Moryu-Io/Bldc_Servo_Driver_Prj/common/ExtInterface/ext_com_define.hpp

#ifndef EXT_COM_DEFINE_HPP
#define EXT_COM_DEFINE_HPP

#include "main.h"

#define IS_REQ_STATUS_SUMMARY(x) ((x & 0x8000) == 0x8000) // REQのCMDIDに15bit目が立っている場合はSummaryを返す
#define EXTRACT_CMD_ID(x) (x & 0x7FFF)

#define CMD_ID_REQ_TORQUE_ON (0x0001)
struct REQ_TORQUE_ON {
  uint8_t u8_doInitialize;
  uint8_t u8_dummy[7];
};

#define CMD_ID_REQ_TORQUE_OFF (0x0002)
struct REQ_TORQUE_OFF {
  uint8_t u8_doTerminate;
  uint8_t u8_dummy[7];
};

#define CMD_ID_REQ_TORQUE_CTRL (0x0003)
struct REQ_TORQUE_CTRL {
  uint8_t u8_doInitialize;
  uint8_t u8_dummy[7];
};

#define CMD_ID_REQ_MOVE_ANGLE (0x0010)
struct REQ_MOVE_ANGLE {
  int32_t  s32_tgt_ang_deg_Q16;
  uint16_t u16_movetime_ms;
  uint16_t u16_currlim_A_Q8;
};

#define CMD_ID_REQ_ANGLE_INIT (0x0011)
struct REQ_ANGLE_INIT {
  uint8_t u8_set_angle_flag;  // 0:現在位置を0とする, 1:指定した角度で初期化する, 最上位bit:強制変更
  uint8_t u8_dummy[3];
  int32_t s32_init_ang_deg_Q16;
};

#define CMD_ID_REQ_SET_TARGET_CURR (0x0110)
struct REQ_SET_TARGET_CURR {
  int32_t s32_target_iq_A_Q16;
  int32_t s32_target_id_A_Q16;
};

#define CMD_ID_RES_STATUS_SUMMARY (0x1000)
struct RES_STATUS_SUMMAY {
  uint8_t b1_motor_driver_fault : 1;
  uint8_t b1_motor_over_temp    : 1;
  uint8_t b1_motor_over_curr    : 1;
  uint8_t b1_motor_torque_on    : 1;
  uint8_t b1_mcu_fault          : 1;
  uint8_t b1_mcu_over_temp      : 1;
  uint8_t b1_dummy_0_67         : 2;
  uint8_t u8_now_mode;
  int16_t s16_out_ang_deg_Q4;
  int8_t  s8_motor_curr_A_Q4;
  int8_t  s8_motor_vol_V_Q3;
  uint8_t u8_vm_V_Q3;
  int8_t  s8_motor_tempr_deg;
};

struct RES_STATUS_SUMMAY2 {
  int32_t s32_out_ang_deg_Q8;
  int8_t  s8_motor_curr_A_Q4;
  int8_t  s8_motor_vol_V_Q3;
  uint8_t u8_vm_V_Q3;
  int8_t  s8_motor_tempr_deg;
};

#define CMD_ID_RES_STATUS_MOVE_ANGLE (0x1001)
struct RES_STATUS_MOVE_ANGLE {
  int16_t  s16_out_ang_deg_Q4;
  int16_t  s16_tgt_ang_deg_Q4;
  uint16_t u16_movetime_ms;
  uint8_t  u8_dummy[2];
};

#define CMD_ID_RES_TEST_COM (0x1234)
struct RES_TEST_COM {
  uint32_t u32_test_const_num;  // 0x12345678
  uint32_t u32_test_count;      // このコマンドをCallするたびにインクリされる
};

union REQ_MESSAGE {
  uint8_t        u8_data[8];
  REQ_TORQUE_ON  reqTrqOn;
  REQ_TORQUE_OFF reqTrqOff;
  REQ_TORQUE_CTRL reqTrqCtrl;
  REQ_MOVE_ANGLE reqMvAng;
  REQ_ANGLE_INIT reqAngIni;
  REQ_SET_TARGET_CURR reqSetTgtCur;
};

union RES_MESSAGE {
  uint8_t               u8_data[8];
  RES_STATUS_SUMMAY     resSummary;
  RES_STATUS_SUMMAY2    resSummary2;
  RES_STATUS_MOVE_ANGLE resStsMvAng;
  RES_TEST_COM          resTestCom;
};

#endif
