Moryu-Io/Bldc_Servo_Driver_Prj/bldc_servo_driver_mini_G4/g431cb_FSDmini/flash_initial_params.cpp

#include "flash_interface.hpp"

const FlashSaveParams C_FlashInitParams __attribute__((aligned(4))) = {
    .var = {
        .u16_fw_ver                  = 0,
        .u16_can_device_id           = 1,
        .s32_elec_angle_offset_CNT   = 0x318,                     // PM3505 default
        .fl_elec_angle_gain_CNTtoDeg = 360.0f * 11.0f / 16384.0f, // PM3505 default
        .s8_elec_angle_dir           = -1,                        // PM3505 default
        .u16_curr_ad_mid_u           = 2048,
        .u16_curr_ad_mid_v           = 2048,
        .u16_curr_ad_mid_w           = 2048,
        .fl_Iq_Pgain                 = 8.0f,
        .fl_Iq_Igain                 = 20000.0f,
        .fl_Iq_Dgain                 = 0.0f,
        .fl_Iq_I_Limit               = 6.0f,
        .fl_Id_Pgain                 = 8.0f,
        .fl_Id_Igain                 = 20000.0f,
        .fl_Id_Dgain                 = 0.0f,
        .fl_Id_I_Limit               = 6.0f,
        .fl_PosCtrl_Pgain            = 0.04f,
        .fl_PosCtrl_Igain            = 0.01f,
        .fl_PosCtrl_Dgain            = 0.0003f,
        .fl_PosCtrl_I_Limit          = 1.0f,
        .fl_PosCtrl_VelLpf_CutOffFrq = 800.0f,
    },
};
