Moryu-Io/Bldc_Servo_Driver_Prj/common/Utility/mymath.cpp

#include "mymath.hpp"

namespace mymath {

#define TABLE_SIXE_ATAN   (577)
#define BLOCK_NUM_ATAN    (26)
#define DEBIDE_ONE_BLOCK_ATAN  (24)

const float atan_table[] = {
	0.0, 0.010757872, 0.021513255, 0.032263662, 0.043006614, 0.053739643, 0.064460294, 0.075166127, 0.085854727, 0.096523698, 0.107170672, 0.117793313, 0.128389314, 0.138956406, 0.149492357, 0.159994976, 0.170462116, 0.180891675, 0.191281599, 0.201629882, 0.211934573, 0.222193772, 0.232405634, 0.242568372,
	0.252680255, 0.25735292, 0.26201412, 0.266663696, 0.271301491, 0.275927351, 0.280541124, 0.285142663, 0.289731822, 0.294308458, 0.298872432, 0.303423606, 0.307961847, 0.312487024, 0.316999008, 0.321497674, 0.3259829, 0.330454567, 0.334912556, 0.339356756, 0.343787055, 0.348203345, 0.352605521, 0.35699348,
	0.361367124, 0.365095906, 0.36881409, 0.372521617, 0.376218433, 0.379904483, 0.383579714, 0.387244075, 0.390897517, 0.39453999, 0.398171448, 0.401791846, 0.405401139, 0.408999285, 0.412586242, 0.416161972, 0.419726435, 0.423279595, 0.426821416, 0.430351863, 0.433870904, 0.437378508, 0.440874644, 0.444359282,
	0.447832397, 0.451109913, 0.454377055, 0.457633802, 0.460880135, 0.464116036, 0.467341488, 0.470556474, 0.473760979, 0.476954988, 0.480138489, 0.483311469, 0.486473916, 0.48962582, 0.492767171, 0.495897961, 0.499018181, 0.502127824, 0.505226885, 0.508315358, 0.511393238, 0.514460523, 0.517517208, 0.520563293,
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
	0.0041832  ,
	0.004471685,
	0.004920121,
	0.005578892,
	0.006545876,
	0.008010219,
	0.01036713 ,
	0.0145673  ,
	0.023503555,
	0.051134668,
	0.034651948,
	0.040277155,
	0.160128443,
	0.39861551 ,
	0.398129858,
	1.193904514,
	2.387445354,
	19.09869013,
	214.859195 ,
	2148.591734,
	21485.91732
}; 

const float atan_table_delimit_val[] =
{
	0.0        ,
	0.25819889 ,
	0.377964473,
	0.480384461,
	0.577350269,
	0.674199862,
	0.774596669,
	0.881917104,
	1.0        ,
	1.133893419,
	1.290994449,
	1.483239697,
	1.732050808,
	2.081665999,
	2.645751311,
	3.872983346,
	4.704630109,
	5.67128182 ,
	9.514364454,
	19.08113669,
	28.63625328,
	57.28996163,
	114.5886501,
	572.9572134,
	5729.577893,
	57295.77951,
	572957.7951
};

float atanf(float x)
{
	int i;
	float index;
	int index_int;
	float index_dec;

	if (x<0) return -atanf(-x);
	if (x == 0.0)   return 0.0;
	for (i = 1; i<=BLOCK_NUM_ATAN; i++)
	{
		if (x <= atan_table_delimit_val[i])
		{
			index = DEBIDE_ONE_BLOCK_ATAN * (i - 1) + ((x - atan_table_delimit_val[i - 1]) / atan_table_width[i - 1]);
			index_int = (int)index;
			index_dec = index - (float)index_int;
			return atan_table[index_int] + index_dec * ((atan_table[index_int + 1] - atan_table[index_int]));
		}
	}
	return atan_table[TABLE_SIXE_ATAN-1];   
}

float atan2f(float y, float x)
{
	if (x >  0.0) return atanf(y / x);
	if (y >= 0.0 &&  x <  0.0) return atanf(y / x) + PI;
	if (y <  0.0 &&  x <  0.0) return atanf(y / x) - PI;
	if (y >  0.0 &&  x == 0.0) return PI / 2.0;
	if (y <  0.0 &&  x == 0.0) return -PI / 2.0;
	if (y == 0.0 &&  x == 0.0) return 0.0;  //普通は定義されない.
	return 0.0;
}


};
